ainnajib2002/Suctiom-Pump-for-Medical-Fluid-Extraction/Desain/Mekanik/Drawing/ScrewM5 x 10 mm, Pitch 0.8 mm Handler.pdf

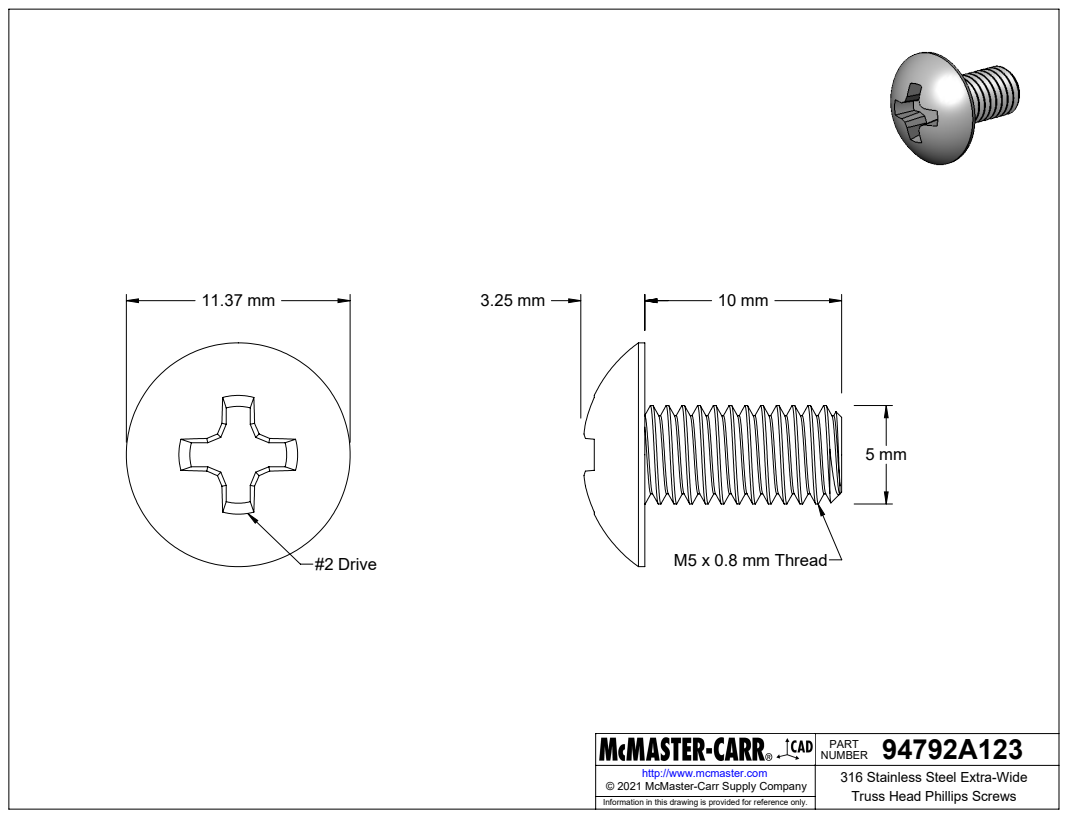
[picture p74: page 1]
#2 Drive; M5 x 0.8 mm Thread

94792A123 PART NUMBER

http://www.mcmaster.com | 316 Stainless Steel Extra-Wide Truss Head Phillips Screws © 2021 McMaster-Carr Supply Company

Information in this drawing is provided for reference only.
